DIYSynthMNL/Pi-Pico-Random-Looping-Sequencer/Hardware/pi-pico-random-looping-sequencer/pi-pico-random-looping-sequencer.kicad_sch

## KiCad design Hardware/pi-pico-random-looping-sequencer/pi-pico-random-looping-sequencer.kicad_sch (2025-03-11)

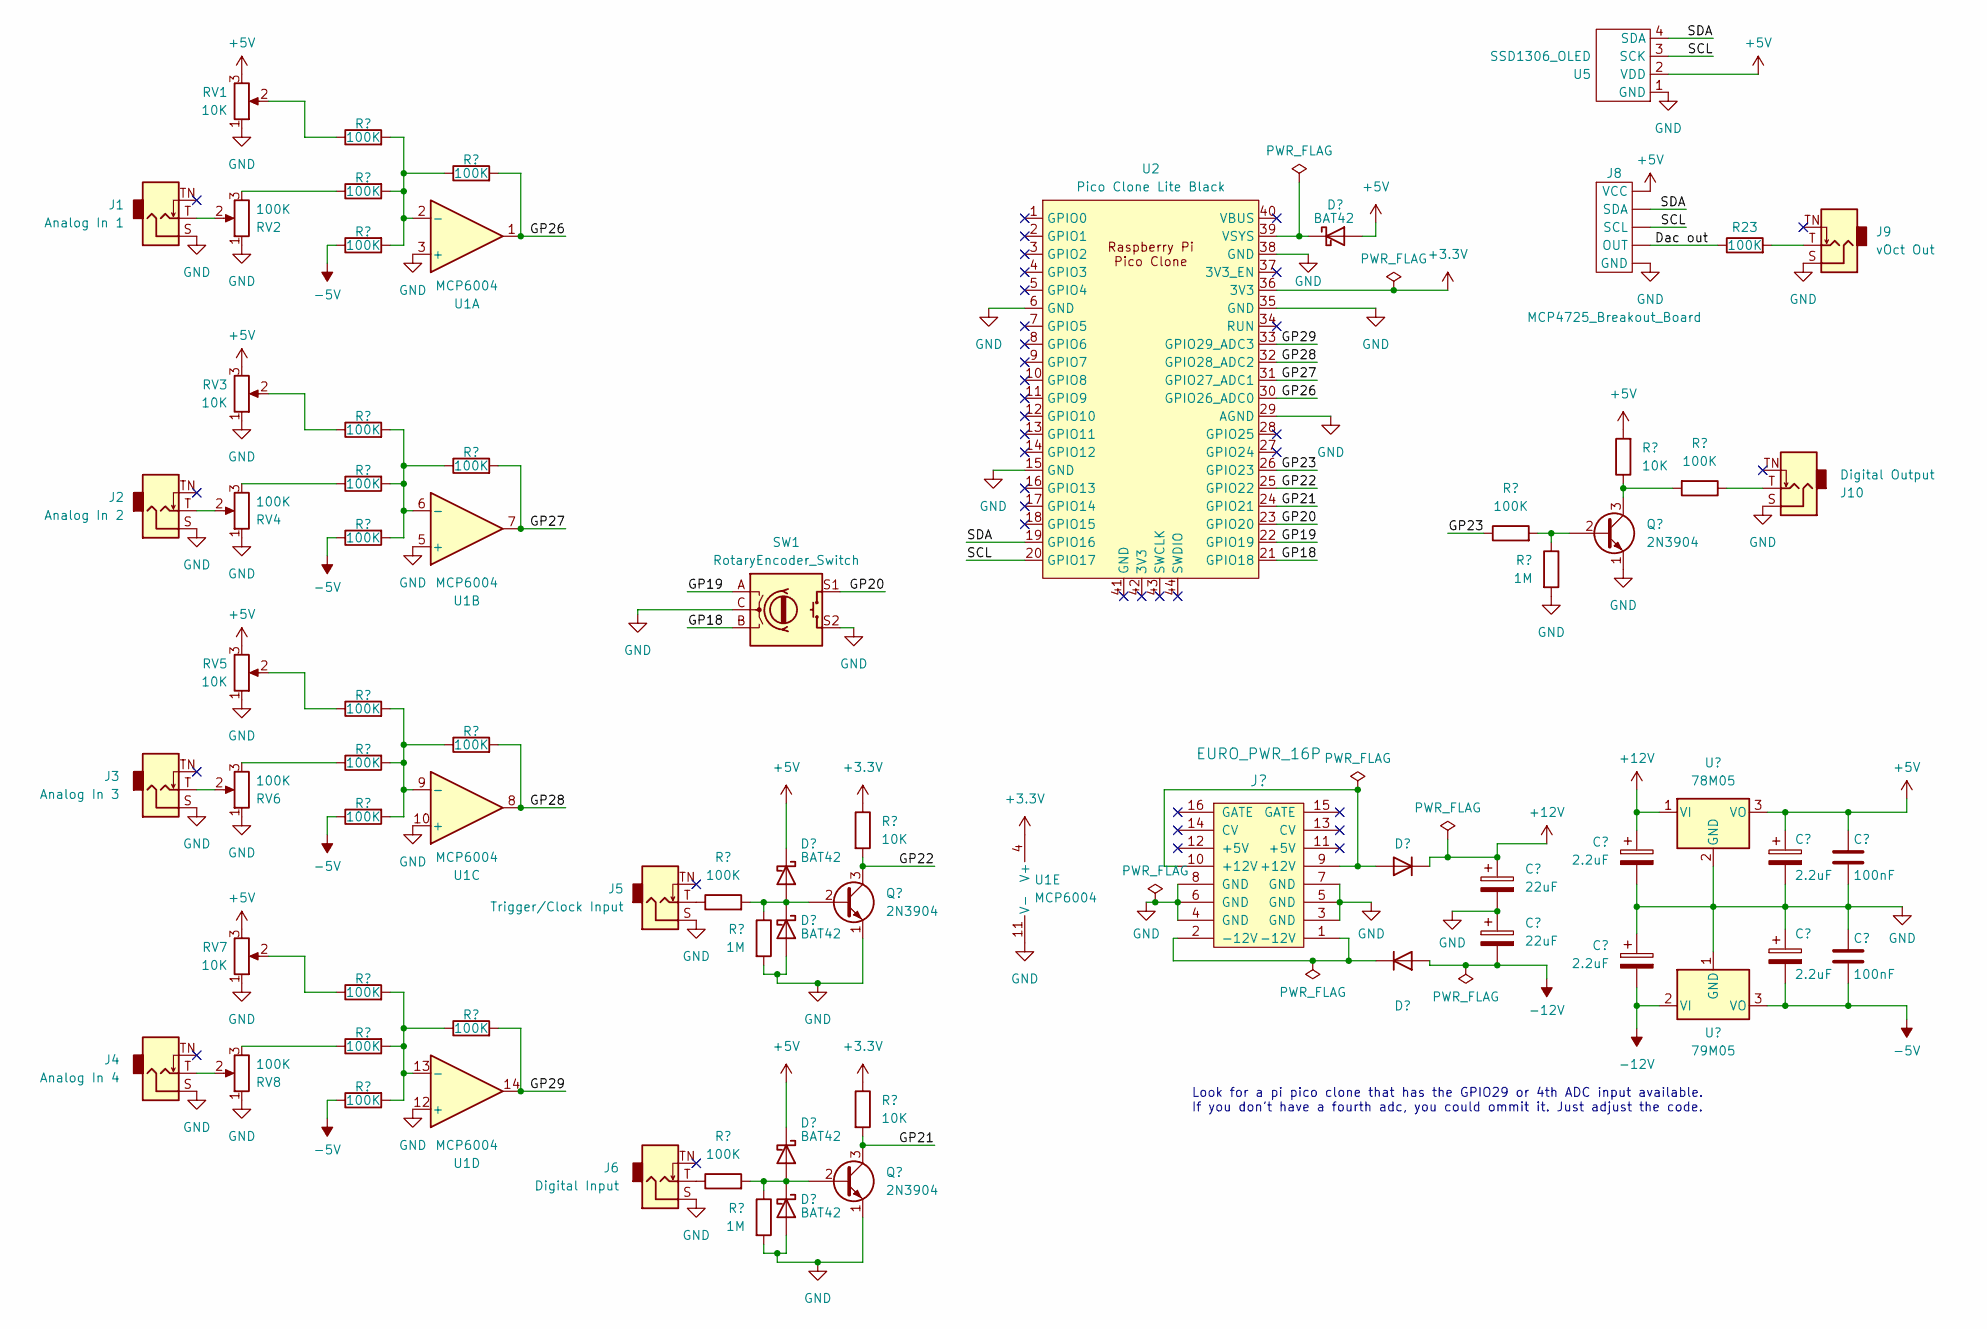
[picture p9: schematic pi-pico-random-looping-sequencer.kicad_sch]

Parts:
C1, C2, C6, C8: 2.2uF; CP_Radial_D5.0mm_P2.50mm
C3, C7: 100nF; C_Rect_L7.0mm_W2.0mm_P5.00mm_BigPads
C4, C5: 22uF; CP_Radial_D4.0mm_P1.50mm
D1, D2, D3, D4, D5: BAT42; D_DO-35_SOD27_P7.62mm_Horizontal
D6, D7: D_DO-41_SOD81_P7.62mm_Horizontal_BigPads
J1: Analog In 1; AudioJack_3.5mm_long_pads
J2: Analog In 2; AudioJack_3.5mm_long_pads
J3: Analog In 3; AudioJack_3.5mm_long_pads
J4: Analog In 4; AudioJack_3.5mm_long_pads
J5: Trigger/Clock Input; AudioJack_3.5mm_long_pads
J6: Digital Input; AudioJack_3.5mm_long_pads
J7: EURO_PWR_16P; IDC-Header_2x08_P2.54mm_Vertical
J8: MCP4725_Breakout_Board
J9: vOct Out; AudioJack_3.5mm_long_pads
J10: Digital Output; AudioJack_3.5mm_long_pads
Q1, Q2, Q3: 2N3904; TO-92_Inline
R1, R2, R3, R4, R5, R6, R7, R8, R9, R10, R11, R12, R13, R14, R15, R16, R18, R21, R25, R26: 100K; R_quarter_watt_L6.3mm_D2.5mm_P7.62mm
R17, R20, R24: 10K; R_quarter_watt_L6.3mm_D2.5mm_P7.62mm
R19, R22, R27: 1M; R_quarter_watt_L6.3mm_D2.5mm_P7.62mm
R23: 100K
RV1, RV3, RV5, RV7: 10K
RV2, RV4, RV6, RV8: 100K
SW1: RotaryEncoder_Switch
U1: MCP6004
U2: Pico Clone Lite Black; RPi_Pico_SMD_TH
U3: 78M05; TO-252-2
U4: 79M05; TO-252-2
U5: SSD1306_OLED

Connections:
+3.3V: R17.1, R20.1, U1.4 (V+), U2.36 (3V3)
+5V: C2.1, C3.1, D1.1 (K), D3.1 (K), D5.2 (A), J8., R24.2, RV1.3, RV3.3, RV5.3, RV7.3, U3.3 (VO), U5.2 (VDD)
+12V: C1.1, C4.1, D6.1 (K), U3.1 (VI)
-5V: C6.2, C7.2, R4.1, R8.1, R12.1, R16.1, U4.3 (VO)
-12V: C5.2, C8.2, D7.2 (A), U4.2 (VI)
Dac out: J8., R23.1
GND: C1.2, C2.2, C3.2, C4.2, C5.1, C6.1, C7.1, C8.1, D2.2 (A), D4.2 (A), J1.S, J2.S, J3.S, J4.S, J5.S, J6.S, J7.3 (GND), J7.4 (GND), J7.5 (GND), J7.6 (GND), J7.7 (GND), J7.8 (GND), J8., J9.S, J10.S, Q1.1 (E), Q2.1 (E), Q3.1 (E), R19.2, R22.2, R27.2, RV1.1, RV2.1, RV3.1, RV4.1, RV5.1, RV6.1, RV7.1, RV8.1, SW1.C, SW1.S2, U1.3 (+), U1.5 (+), U1.10 (+), U1.11 (V-), U1.12 (+), U2.6 (GND), U2.15 (GND), U2.29 (AGND), U2.35 (GND), U2.38 (GND), U3.2 (GND), U4.1 (GND), U5.1 (GND)
GP18: SW1.B, U2.21 (GPIO18)
GP19: SW1.A, U2.22 (GPIO19)
GP20: SW1.S1, U2.23 (GPIO20)
GP21: Q2.3 (C), R20.2, U2.24 (GPIO21)
GP22: Q1.3 (C), R17.2, U2.25 (GPIO22)
GP23: R26.1, U2.26 (GPIO23)
GP26: R2.2, U1.1, U2.30 (GPIO26_ADC0)
GP27: R6.2, U1.7, U2.31 (GPIO27_ADC1)
GP28: R10.2, U1.8, U2.32 (GPIO28_ADC2)
GP29: R14.2, U1.14, U2.33 (GPIO29_ADC3)
unnamed: D1.2 (A), D2.1 (K), Q1.2 (B), R18.2, R19.1
unnamed: D3.2 (A), D4.1 (K), Q2.2 (B), R21.2, R22.1
unnamed: D5.1 (K), U2.39 (VSYS)
unnamed: D6.2 (A), J7.9 (+12V), J7.10 (+12V)
unnamed: D7.1 (K), J7.1 (-12V), J7.2 (-12V)
unnamed: J1.T, RV2.2
unnamed: J2.T, RV4.2
unnamed: J3.T, RV6.2
unnamed: J4.T, RV8.2
unnamed: J5.T, R18.1
unnamed: J6.T, R21.1
unnamed: J9.T, R23.2
unnamed: J10.T, R25.1
unnamed: Q3.2 (B), R26.2, R27.1
unnamed: Q3.3 (C), R24.1, R25.2
unnamed: R1.1, RV1.2
unnamed: R1.2, R2.1, R3.2, R4.2, U1.2 (-)
unnamed: R3.1, RV2.3
unnamed: R5.1, RV3.2
unnamed: R5.2, R6.1, R7.2, R8.2, U1.6 (-)
unnamed: R7.1, RV4.3
unnamed: R9.1, RV5.2
unnamed: R9.2, R10.1, R11.2, R12.2, U1.9 (-)
unnamed: R11.1, RV6.3
unnamed: R13.1, RV7.2
unnamed: R13.2, R14.1, R15.2, R16.2, U1.13 (-)
unnamed: R15.1, RV8.3
SCL: J8., U2.20 (GPIO17), U5.3 (SCK)
SDA: J8., U2.19 (GPIO16), U5.4 (SDA)

Notes on the sheet:
Look for a pi pico clone that has the GPIO29 or 4th ADC input available. If you don't have a fourth adc, you could ommit it. Just adjust the code.
